TinkerDoge/DogePet/sectors/src/Sensors.cpp

#include "Sensors.h"

namespace Sectors { namespace Sensors {
  static bool inited = false;

  void begin() {
    if (inited) return;
    // Touch/button pins can be initialized here in future
    // For now, rely on existing sketch setup
    inited = true;
  }

  void update() {
    if (!inited) return;
    // Placeholder for polling touch/button with debouncing
  }
}}
